Rex--/powerpic/firmware/src/drivers/uart.c

/** @file uart.c
 *
 * UART driver for PIC16LF1919x on Hardware EUSART1
 *
 * This driver implements an 8-byte buffer for both receiving and transmitting.
 * Function are provided that interface with the standard library `stdio.h`.
 * After setup of the driver, you are encouraged to use the `printf()` and
 * `scanf()` functions from the standard library.
*/

#include <stdint.h>
#include <xc.h>

#include "drivers/uart.h"

#define UART_TX_BUFFER_SIZE    8    /**< Length of UART transmit buffer in bytes */
#define UART_RX_BUFFER_SIZE    8    /**< Length of UART receive buffer in bytes */


static volatile uint8_t uart_tx_buffer_head = 0;
static volatile uint8_t uart_tx_buffer_tail = 0;
static volatile uint8_t uart_tx_buffer_remaining = 0;
static volatile uint8_t uart_tx_buffer[UART_TX_BUFFER_SIZE] = {0};

static volatile uint8_t uart_rx_buffer_head = 0;
static volatile uint8_t uart_rx_buffer_tail = 0;
static volatile uint8_t uart_rx_buffer_remaining = 0;
static volatile uint8_t uart_rx_buffer[UART_RX_BUFFER_SIZE] = {0};


/**
 * Initialize the UART driver with default settings.
 * Currently supports no configuration options. Assumes a 1MHz clock speed and
 * 9600 baud serial connection. After this is called standard i/o functions from
 * stdio.h can be used such as printf().
 * 
 * @returns 0 if initialized, <0 if an error occurred.
*/
int
uart_init (void)
{
    // Before configuring the USART module, the PORT pins need to be configured
    // as well as the Peripherial Pin Select (PPS) module.
    // Currently the pins used aren't configurable, they are:
    // - RX: RC2
    // - TX: RC3
    //
    TRISCbits.TRISC3 = 0;   // Set RC3(TX) as output
    RC3PPS = 0x0D;          // x0D is the value for TX for USART1

    TRISCbits.TRISC2 = 1;   // Set RC2 as input
    ANSELCbits.ANSC2 = 0;   // Disable analog input
    RX1PPS = 0x12;          // 0x12 is the value for RC2

    // The following registers control the baudrate generation for the EUSART 1
    // module:
    // BAUD1CON - Baud rate control register
    //   ABDOVF:0 | RCIDL:1:r | 0 | SCKP:0 | BRG16:0 | 0 | WUE:0 | ABDEN: 0
    //     BRG16  - 16-bit Baud Rate Generator
    // SP1BRG - Baud Rate Generator value
    //   SP1BRGH | SP1BRGL
    //     SP1BRGL  - Lower 8-bits of the Baud Rate Generator
    //     SP1BRGH  - Upper 8-bits of the Baud Rate Generator
    // 
    // We want to use the 16-bit generator and set SP1BRG to 25 to achieve our
    // desired baud of 9615 @ 1MHz clock speed- which is close enough to 9600.
    //
    BAUD1CON = 0b01001000;
    SP1BRG = 25;

    // The following registers configure the Transmit and Receive modules:
    // 
    // TX1STA - Transmit status and control register
    //   0 | TX9:0 | TXEN:0 | SYNC:0 | 0 | BRGH:0 | TRMT:1:r | TX9D:0
    //     TXEN - Transmit Enable Bit
    //     BRGH - High Baud Rate Select Bit
    // RC1STA - Receive status
    //  and control register
    //   SPEN:0 | RX9:0 | 0 | CREN:0 | ADDEN:0 | FERR:0:r | OERR:0:r | RX9D:0:r
    //     SPEN - Serial Port Enable Bit
    //     CREN - Continuous Receive Enable Bit
    // 
    // RC1STA.SPEN enables the USART Module, so configure TX first.
    // We want to use the 16-bit Baud Rate Generator so set BRGH.^
    //   ( Maybe we should set that bit above ^ )
    //
    TX1STA = 0b00100100;
    RC1STA = 0b10010000;

    // Set up the default driver state.
    //
    uart_tx_buffer_head = 0;
    uart_tx_buffer_tail = 0;
    uart_tx_buffer_remaining = sizeof(uart_tx_buffer);

    uart_rx_buffer_head = 0;
    uart_rx_buffer_tail = 0;
    uart_rx_buffer_remaining = 0;

    // Enable Receive interrupt
    //
    PIE3bits.RC1IE = 1;

    // TODO: Add some error checking to make sure USART Module has actually been
    // enabled and is ready for use.
    //
    return 0;
}   /* uart_init() */


/**
 * Write a byte of data to the currently configured UART.
 * 
 * This driver provides an 8-byte receive buffer in addition to the hardware
 * module's 1-byte buffer.
 * 
 * @param[in] data The data byte to be written.
*/
void
uart_write (uint8_t data)
{
    // If the TX1IE is not set transmission interrupts have been disabled.
    // They are only enabled when we have previously written to TX1REG, so if
    // they are disabled we can immediatly write this byte to the TX1REG.
    //
    if (0 == PIE3bits.TX1IE)
    {
        TX1REG = data;
    }

    // If the TX1IE bit is set it means we have some data in tx_buffer already
    // queued up. If there's room we add it tx_buffer, if not we block and wait.
    //
    else
    {
        while (0 == uart_tx_buffer_remaining)
        {
            // Wait until there is room in the buffer. This should take max the
            // amount of time to transmit a single byte.
        }

        // Disable the TX interrupt before adding our data to the buffer.
        //
        PIE3bits.TX1IE = 0;

        uart_tx_buffer[uart_tx_buffer_head] = data;

        // Next we increment the tx_buffer_head, wrapping around if neccessary,
        // and decrement tx_buffer_remaining.
        //
        uart_tx_buffer_head++;
        if (sizeof(uart_tx_buffer) <= uart_tx_buffer_head)
        {
            uart_tx_buffer_head = 0;
        }
        uart_tx_buffer_remaining--;

    }

    // Enable the transmission interrupt- meaning we have more data in the
    // buffer to send.
    //
    PIE3bits.TX1IE = 1;

    return;
}   /* uart_write() */


/**
 * Read a byte of data from the currently configured UART.
 * 
 * This driver provides an 8-byte receive buffer in addition to the hardware
 * module's 2-byte buffer.
 * 
 * @returns The byte of data that was read.
*/
uint8_t
uart_read (void)
{
    uint8_t data = 0;

    while (0 == uart_rx_buffer_remaining)
    {
        // Block and wait if we don't have any data in the rx_buffer
    }

    data = uart_rx_buffer[uart_rx_buffer_tail];

    // Increment rx_buffer_tail, wrapping if neccessary.
    //
    uart_rx_buffer_tail++;
    if (sizeof(uart_rx_buffer) <= uart_rx_buffer_tail)
    {
        uart_rx_buffer_tail = 0;
    }

    // Disable interrupts while we change the amount remaining.
    //
    PIE3bits.RC1IE = 0;
    uart_rx_buffer_remaining--;
    PIE3bits.RC1IE = 1;

    return data;
}


/**
 * The Interrupt Service Handler for the Transmit Interrupt Flag.
 * 
 * This handles writing of data to TX1REG from the uart_tx_buffer. It should be
 * called by the main ISR when TX1IE is enabled and TX1IF is triggered.
*/
void
uart_tx_isr (void)
{
    // Check if there is any data in the tx_buffer
    //
    if (sizeof(uart_tx_buffer) > uart_tx_buffer_remaining)
    {
        // Write the tail to TX1REG
        //
        TX1REG = uart_tx_buffer[uart_tx_buffer_tail];

        // Increment tx_buffer_tail, wrapping around if neccessary.
        //
        uart_tx_buffer_tail++;
        if (sizeof(uart_tx_buffer) <= uart_tx_buffer_tail)
        {
            uart_tx_buffer_tail = 0;
        }
        uart_tx_buffer_remaining++;
    }
    // If the buffer is empty, disable the Transmit Interrupt.
    //
    else
    {
        PIE3bits.TX1IE = 0;
    }

    return;
}   /* uart_tx_isr() */


/**
 * The Interrupt Service Handler for the Receive Interrupt Flag.
 * 
 * This handles reading of the RC1REG register into rx_buffer. It should be
 * called by the main ISR when RC1IE is enabled and RC1IF is triggered.
*/
void
uart_rx_isr (void)
{
    // Read a byte of data from the receive register
    //
    uart_rx_buffer[uart_rx_buffer_head] = RC1REG;

    // Increment rx_buffer_head
    //
    uart_rx_buffer_head++;
    if (sizeof(uart_tx_buffer) <= uart_rx_buffer_head)
    {
        uart_rx_buffer_head = 0;
    }
    uart_rx_buffer_remaining++;
}   /* uart_rx_isr() */


/**
 * This implements an interface for the standard library stdio.h to hook into.
 * 
 * Stub wrapper for uart_write().
 * 
 * @param[in] data Data byte to be written.
*/
void
putch (uint8_t data)
{
    uart_write(data);
    return;
}   /* putch() */

/**
 * This implements an interface for the standard library stdio.h to hook into.
 * 
 * Stub wrapper for uart_read().
 * 
 * @returns The byte of data read. Blocks if no data available.
*/
int
getch (void)
{
    return abs(uart_read());
}   /* getch() */


/*** EOF ***/
